AnotherBuildCorner/Relay_Switcher/Photos/Screenshot 2024-06-09 212933.png

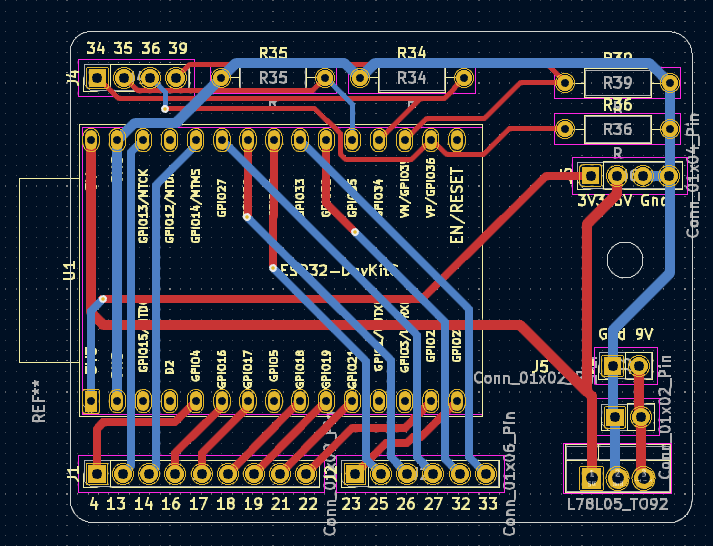
Photos/Screenshot 2024-06-09 212933.png
