AnotherBuildCorner/Relay_Switcher/Photos/Screenshot 2024-06-09 213035.png

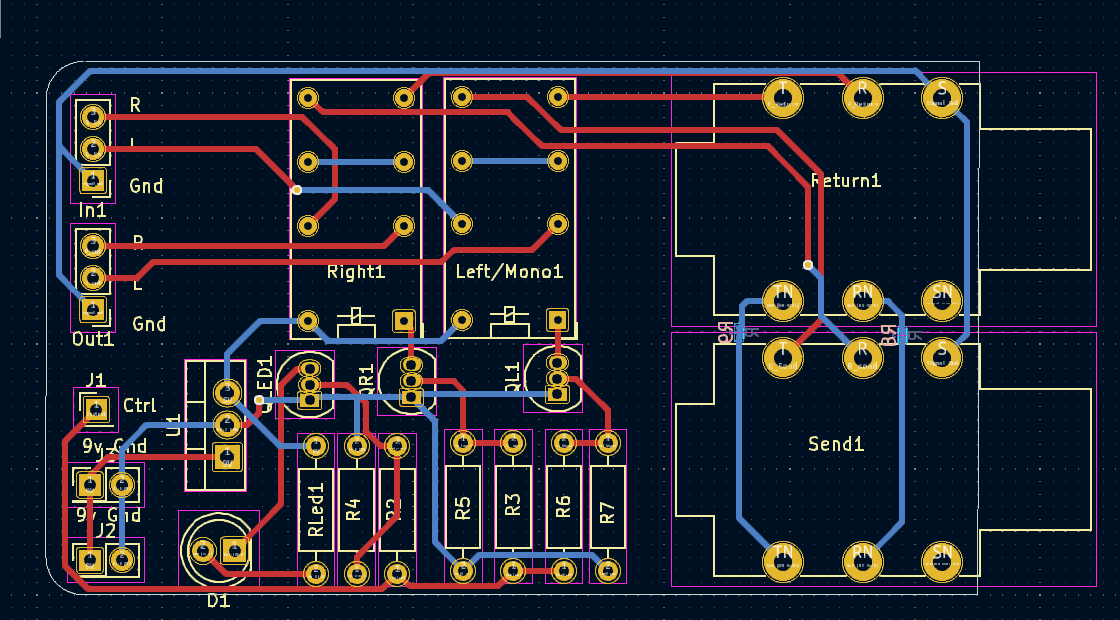
Photos/Screenshot 2024-06-09 213035.png
