AnotherBuildCorner/Relay_Switcher/Photos/Screenshot 2024-06-09 213115.png

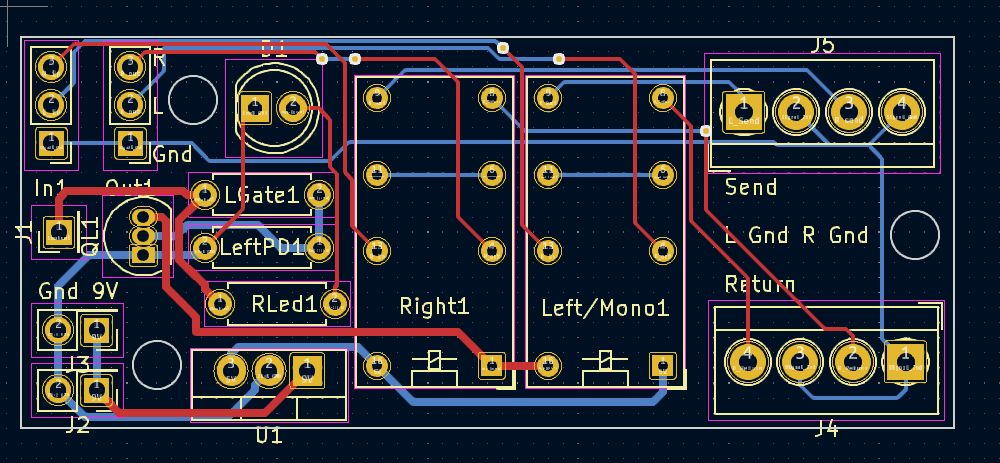
Photos/Screenshot 2024-06-09 213115.png
