AnotherBuildCorner/Relay_Switcher/Photos/Screenshot 2024-06-09 213131.png

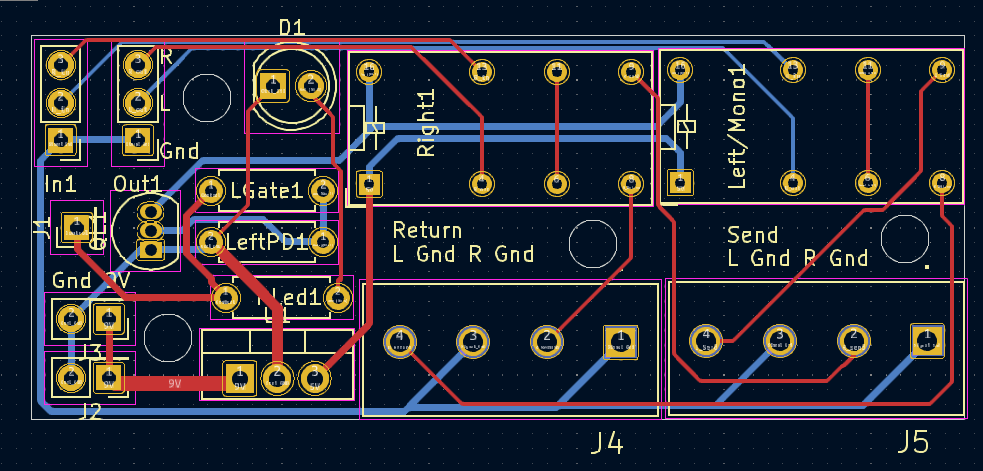
Photos/Screenshot 2024-06-09 213131.png
