AnotherBuildCorner/Relay_Switcher/Photos/V3 Jackless Input only.png

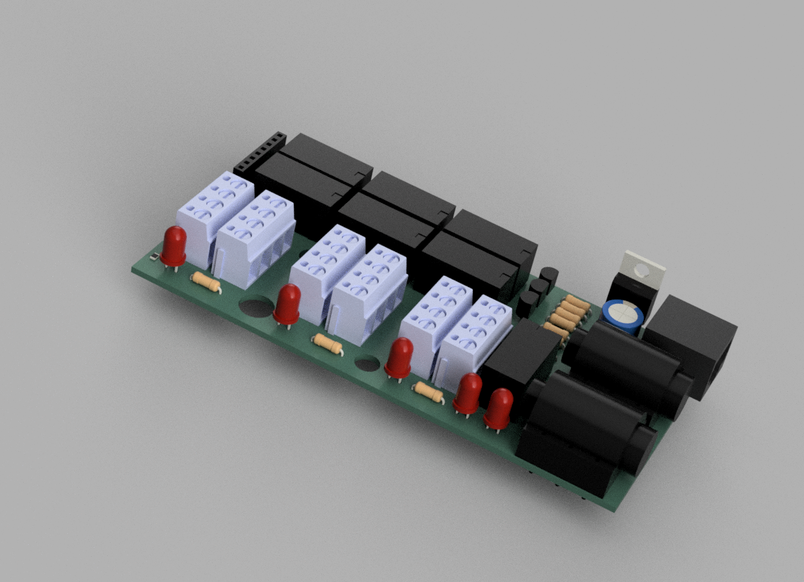
Photos/V3 Jackless Input only.png
