AnotherBuildCorner/Relay_Switcher/PCB's/Loop Board V3 Jackless/Loop Board 3 Jackless Input/Loop Board 3 Jackless Input.step

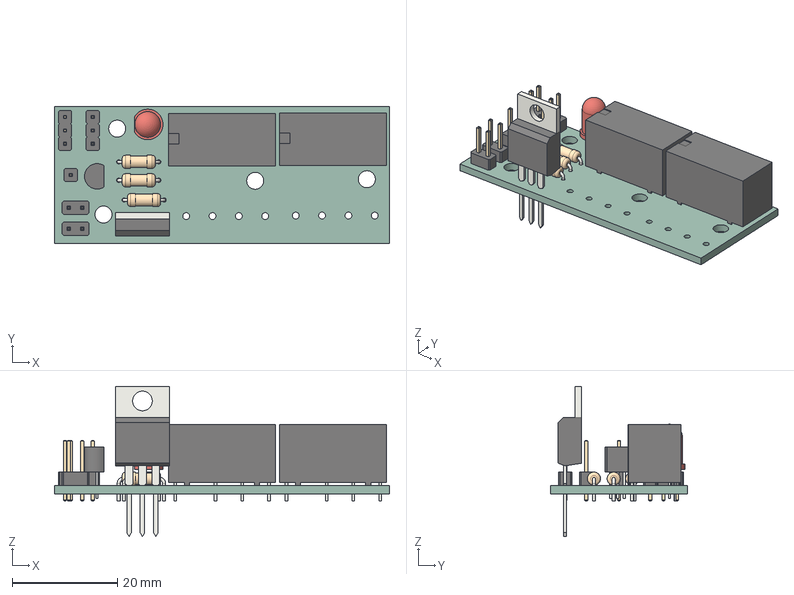
[picture p34: CAD file, 2024-06-10]
PCB's/Loop Board V3 Jackless/Loop Board 3 Jackless Input/Loop Board 3 Jackless Input.step
63.6 x 26.0 x 28.5 mm
PedalboardMain PCB
