AnotherBuildCorner/Relay_Switcher/3D Print Models/8 Switch Footswitch/8 bay back.stl

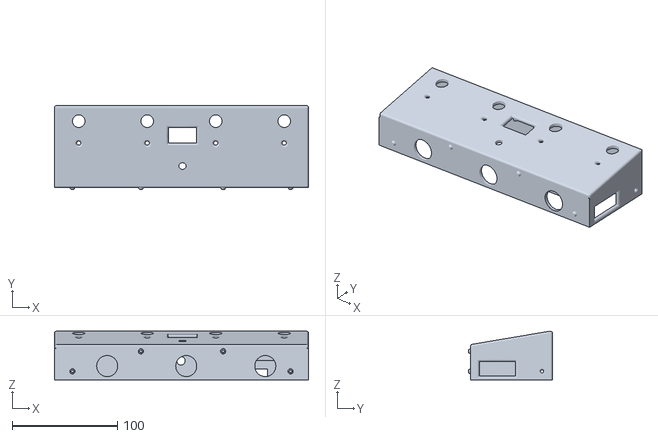
[picture p35: CAD file, 2024-07-15]
3D Print Models/8 Switch Footswitch/8 bay back.stl
241.0 x 80.0 x 46.0
