AnotherBuildCorner/Relay_Switcher/3D Print Models/V3 Jackless/6 Bay Long models/Base.stl

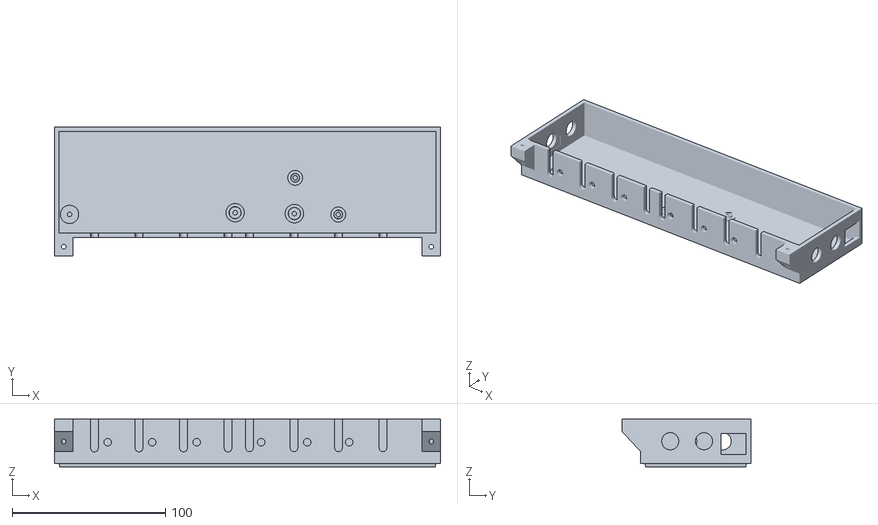
[picture p36: CAD file, 2024-07-15]
3D Print Models/V3 Jackless/6 Bay Long models/Base.stl
251.5 x 84.0 x 31.0
