AnotherBuildCorner/Relay_Switcher/3D Print Models/V3 Jackless/6 Bay Stack models/Lid.stl

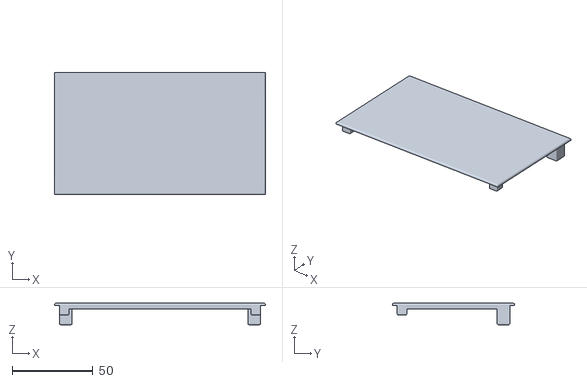
[picture p37: CAD file, 2024-07-15]
3D Print Models/V3 Jackless/6 Bay Stack models/Lid.stl
131.0 x 76.0 x 13.5
