AnotherBuildCorner/Relay_Switcher/3D Print Models/V3 Jackless/6 Bay Stack models/Bottom-output.stl

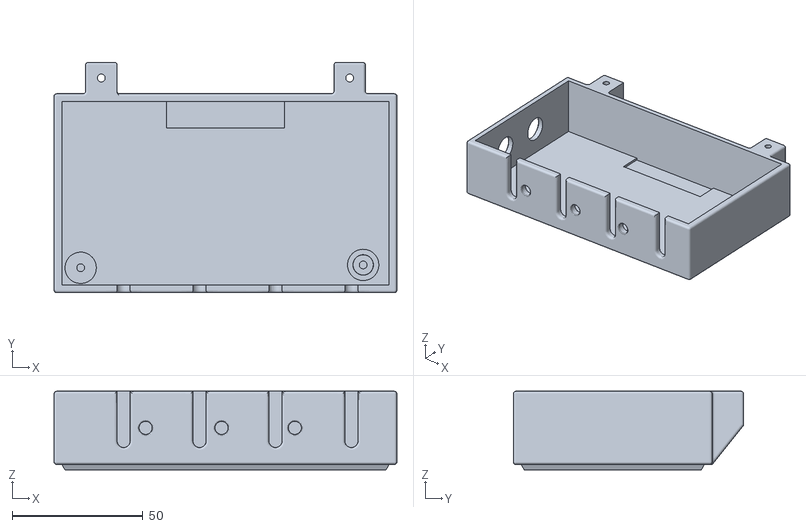
[picture p38: CAD file, 2024-07-15]
3D Print Models/V3 Jackless/6 Bay Stack models/Bottom-output.stl
131.0 x 88.0 x 30.0
