AnotherBuildCorner/Relay_Switcher/PCB's/8P breakout header/8P breakout header.kicad_pcb

## KiCad design PCB's/8P breakout header/8P breakout header.kicad_pcb (2024-06-09)

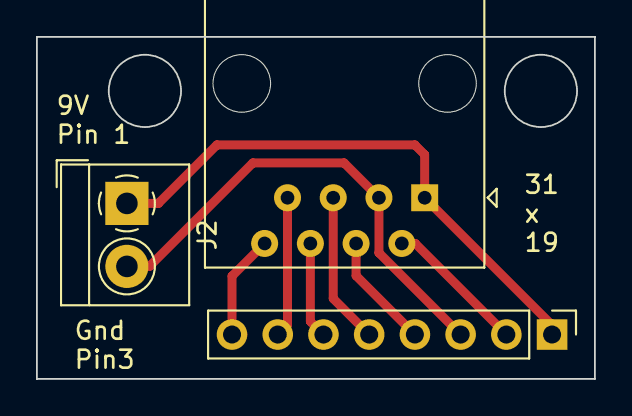
[picture p60: board PCB's/8P breakout header/8P breakout header.kicad_pcb from above]

Board: 2 copper layers, 31.0 x 19.0 mm, 3 parts (0 on the bottom side), 8 nets.

Parts:
J1: 8P8C; RJ45_Amphenol_54602-x08_Horizontal
J2: Screw_Terminal_01x02; TerminalBlock_4Ucon_1x02_P3.50mm_Horizontal
J4: Conn_01x08_Pin; PinHeader_1x08_P2.54mm_Vertical

Connections:
unnamed: J1.1, J2.1, J4.1
unnamed: J1.3, J2.2, J4.3
unnamed: J1.2, J4.2
unnamed: J1.4, J4.4
unnamed: J1.5, J4.5
unnamed: J1.6, J4.6
unnamed: J1.7, J4.7
unnamed: J1.8, J4.8
