AnotherBuildCorner/Relay_Switcher/PCB's/8P breakout header/8P breakout header panel/8P breakout header.kicad_pcb

## KiCad design PCB's/8P breakout header/8P breakout header panel/8P breakout header.kicad_pcb (2024-06-09)

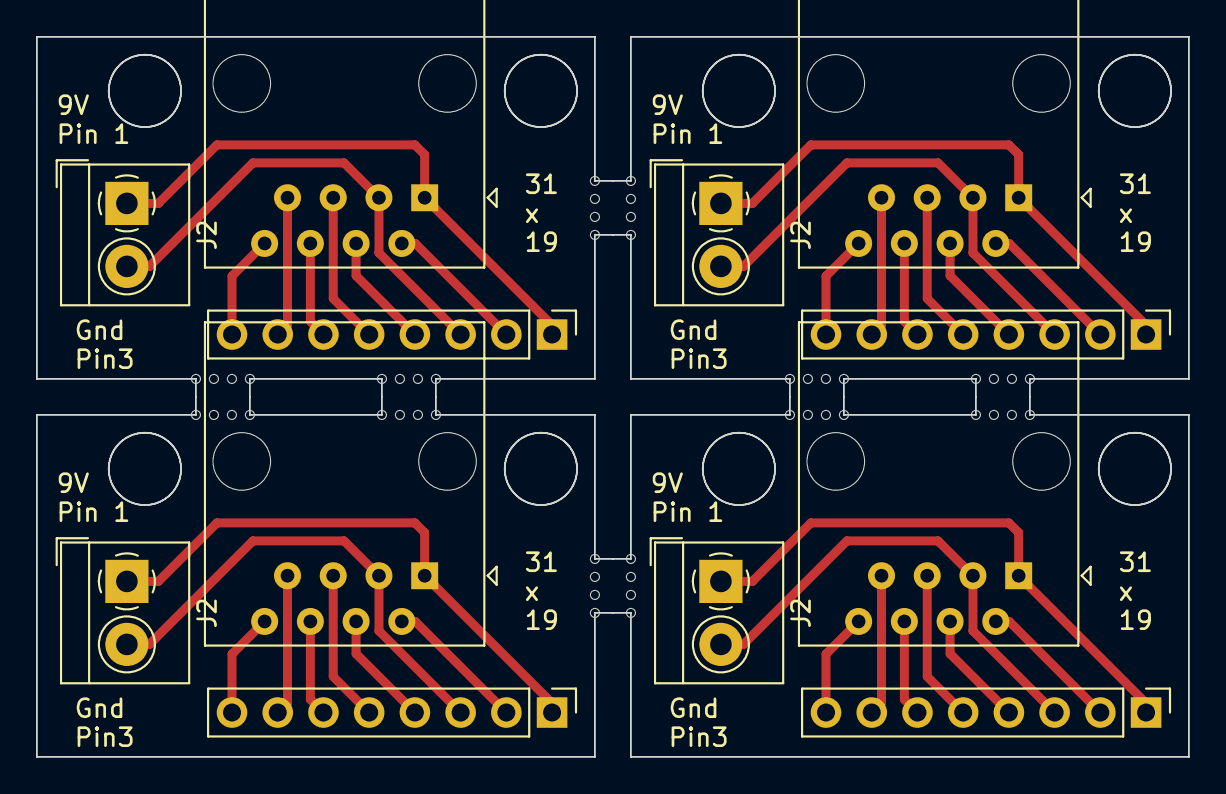
[picture p61: board PCB's/8P breakout header/8P breakout header panel/8P breakout header.… from above]

Board: 2 copper layers, 64.0 x 40.0 mm, 60 parts (0 on the bottom side), 32 nets.

Parts:
J1, J1#2, J1#3, J1#4: 8P8C; RJ45_Amphenol_54602-x08_Horizontal
J2, J2#2, J2#3, J2#4: Screw_Terminal_01x02; TerminalBlock_4Ucon_1x02_P3.50mm_Horizontal
J4, J4#2, J4#3, J4#4: Conn_01x08_Pin; PinHeader_1x08_P2.54mm_Vertical
KiKit_MB_1_1, KiKit_MB_1_2, KiKit_MB_1_3, KiKit_MB_1_4, KiKit_MB_2_1, KiKit_MB_2_2, KiKit_MB_2_3, KiKit_MB_2_4, KiKit_MB_3_1, KiKit_MB_3_2, KiKit_MB_3_3, KiKit_MB_3_4, KiKit_MB_4_1, KiKit_MB_4_2, KiKit_MB_4_3, KiKit_MB_4_4, KiKit_MB_5_1, KiKit_MB_5_2, KiKit_MB_5_3, KiKit_MB_5_4, KiKit_MB_6_1, KiKit_MB_6_2, KiKit_MB_6_3, KiKit_MB_6_4, KiKit_MB_7_1, KiKit_MB_7_2, KiKit_MB_7_3, KiKit_MB_7_4, KiKit_MB_8_1, KiKit_MB_8_2, KiKit_MB_8_3, KiKit_MB_8_4, KiKit_MB_9_1, KiKit_MB_9_2, KiKit_MB_9_3, KiKit_MB_9_4, KiKit_MB_10_1, KiKit_MB_10_2, KiKit_MB_10_3, KiKit_MB_10_4, KiKit_MB_11_1, KiKit_MB_11_2, KiKit_MB_11_3, KiKit_MB_11_4, KiKit_MB_12_1, KiKit_MB_12_2, KiKit_MB_12_3, KiKit_MB_12_4: NPTH

Connections:
Board_0-Net-(J2-Pin_1): J1#3.1, J2#3.1, J4#4.1
Board_0-Net-(J2-Pin_2): J1#3.3, J2#3.2, J4#4.3
Board_0-Net-(J4-Pin_2): J1#3.2, J4#4.2
Board_0-Net-(J4-Pin_4): J1#3.4, J4#4.4
Board_0-Net-(J4-Pin_5): J1#3.5, J4#4.5
Board_0-Net-(J4-Pin_6): J1#3.6, J4#4.6
Board_0-Net-(J4-Pin_7): J1#3.7, J4#4.7
Board_0-Net-(J4-Pin_8): J1#3.8, J4#4.8
Board_1-Net-(J2-Pin_1): J1#2.1, J2.1, J4#3.1
Board_1-Net-(J2-Pin_2): J1#2.3, J2.2, J4#3.3
Board_1-Net-(J4-Pin_2): J1#2.2, J4#3.2
Board_1-Net-(J4-Pin_4): J1#2.4, J4#3.4
Board_1-Net-(J4-Pin_5): J1#2.5, J4#3.5
Board_1-Net-(J4-Pin_6): J1#2.6, J4#3.6
Board_1-Net-(J4-Pin_7): J1#2.7, J4#3.7
Board_1-Net-(J4-Pin_8): J1#2.8, J4#3.8
Board_2-Net-(J2-Pin_1): J1.1, J2#4.1, J4.1
Board_2-Net-(J2-Pin_2): J1.3, J2#4.2, J4.3
Board_2-Net-(J4-Pin_2): J1.2, J4.2
Board_2-Net-(J4-Pin_4): J1.4, J4.4
Board_2-Net-(J4-Pin_5): J1.5, J4.5
Board_2-Net-(J4-Pin_6): J1.6, J4.6
Board_2-Net-(J4-Pin_7): J1.7, J4.7
Board_2-Net-(J4-Pin_8): J1.8, J4.8
Board_3-Net-(J2-Pin_1): J1#4.1, J2#2.1, J4#2.1
Board_3-Net-(J2-Pin_2): J1#4.3, J2#2.2, J4#2.3
Board_3-Net-(J4-Pin_2): J1#4.2, J4#2.2
Board_3-Net-(J4-Pin_4): J1#4.4, J4#2.4
Board_3-Net-(J4-Pin_5): J1#4.5, J4#2.5
Board_3-Net-(J4-Pin_6): J1#4.6, J4#2.6
Board_3-Net-(J4-Pin_7): J1#4.7, J4#2.7
Board_3-Net-(J4-Pin_8): J1#4.8, J4#2.8
