AnotherBuildCorner/Relay_Switcher/PCB's/Coms Board V1/PedalboardBrain.kicad_pcb

## KiCad design PCB's/Coms Board V1/PedalboardBrain.kicad_pcb (2024-06-09, an earlier design)

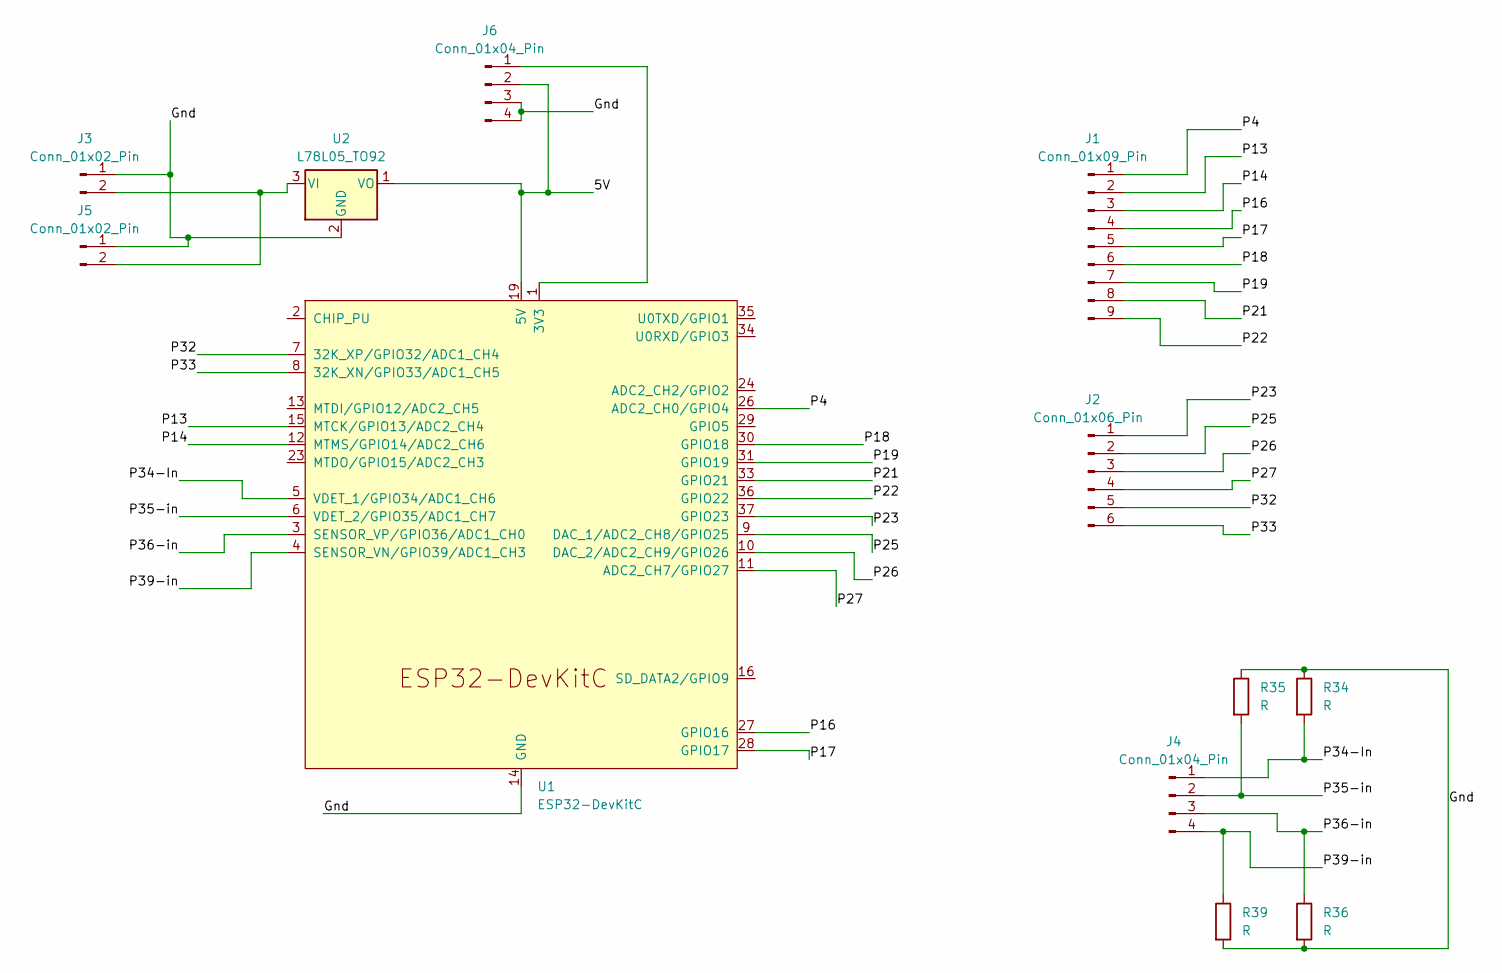
[picture p62: schematic PedalboardBrain.kicad_sch]

Parts:
J1: Conn_01x09_Pin; PinHeader_1x09_P2.54mm_Vertical
J2: Conn_01x06_Pin; PinHeader_1x06_P2.54mm_Vertical
J3, J5: Conn_01x02_Pin; PinHeader_1x02_P2.54mm_Vertical
J4, J6: Conn_01x04_Pin; PinHeader_1x04_P2.54mm_Vertical
R34, R35, R36, R39: R; R_Axial_DIN0207_L6.3mm_D2.5mm_P10.16mm_Horizontal
U1: ESP32-DevKitC; ESP32-DevKitC_30Pin
U2: L78L05_TO92; TO-220-3_Vertical

Connections:
/5V: J6.2, U1.19 (5V), U2.1 (VO)
/Gnd: J3.1, J5.1, J6.3, J6.4, R34.1, R35.1, R36.2, R39.2, U1.14 (GND), U1.32 (GND), U1.38 (GND), U2.2 (GND)
/P4: J1.1, U1.26 (ADC2_CH0/GPIO4)
/P13: J1.2, U1.15 (MTCK/GPIO13/ADC2_CH4)
/P14: J1.3, U1.12 (MTMS/GPIO14/ADC2_CH6)
/P16: J1.4, U1.27 (GPIO16)
/P17: J1.5, U1.28 (GPIO17)
/P18: J1.6, U1.30 (GPIO18)
/P19: J1.7, U1.31 (GPIO19)
/P21: J1.8, U1.33 (GPIO21)
/P22: J1.9, U1.36 (GPIO22)
/P23: J2.1, U1.37 (GPIO23)
/P25: J2.2, U1.9 (DAC_1/ADC2_CH8/GPIO25)
/P26: J2.3, U1.10 (DAC_2/ADC2_CH9/GPIO26)
/P27: J2.4, U1.11 (ADC2_CH7/GPIO27)
/P32: J2.5, U1.7 (32K_XP/GPIO32/ADC1_CH4)
/P33: J2.6, U1.8 (32K_XN/GPIO33/ADC1_CH5)
/P34-In: J4.1, R34.2, U1.5 (VDET_1/GPIO34/ADC1_CH6)
/P35-in: J4.2, R35.2, U1.6 (VDET_2/GPIO35/ADC1_CH7)
/P36-in: J4.3, R36.1, U1.3 (SENSOR_VP/GPIO36/ADC1_CH0)
/P39-in: J4.4, R39.1, U1.4 (SENSOR_VN/GPIO39/ADC1_CH3)
unnamed: J3.2, J5.2, U2.3 (VI)
unnamed: J6.1, U1.1 (3V3)

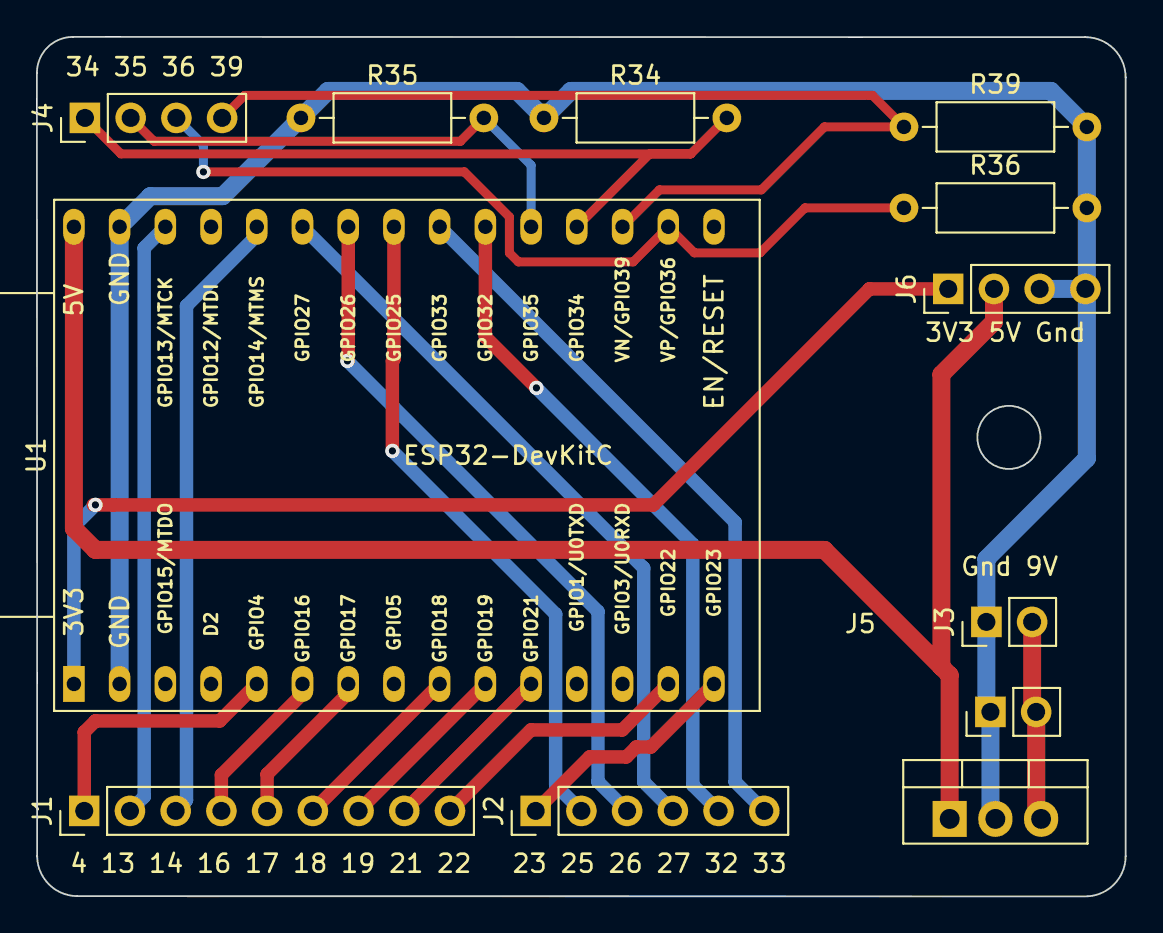
[picture p63: board PedalboardBrain.kicad_pcb from above]

Board: 2 copper layers, 60.5 x 47.8 mm, 12 parts (0 on the bottom side), 23 nets.
