AnotherBuildCorner/Relay_Switcher/PCB's/Coms Board V2/Coms Board V2.kicad_pcb

## KiCad design PCB's/Coms Board V2/Coms Board V2.kicad_pcb (2024-06-08)

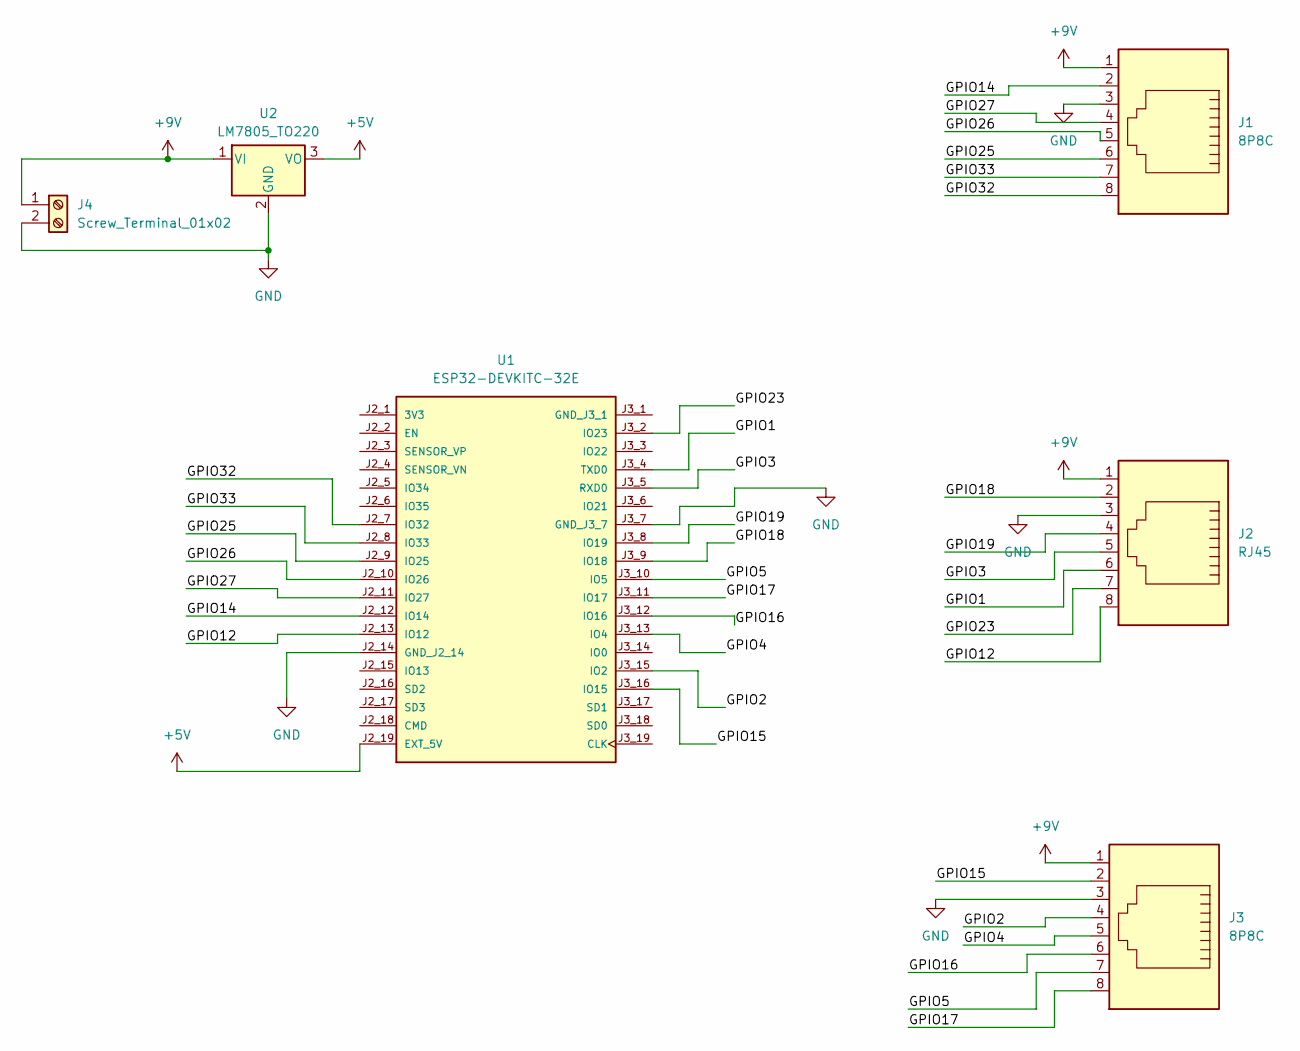
[picture p64: schematic Coms Board V2.kicad_sch]

Parts:
J1, J3: 8P8C; RJ45_Amphenol_54602-x08_Horizontal
J2: RJ45; RJ45_Amphenol_54602-x08_Horizontal
J4: Screw_Terminal_01x02; TerminalBlock_Altech_AK300-2_P5.00mm
U1: ESP32-DEVKITC-32E; MODULE_ESP32-DEVKITC-32E; PARTREV 1.4
U2: LM7805_TO220; TO-220-3_Vertical

Connections:
+5V: U1.J2_19 (EXT_5V), U2.3 (VO)
+9V: J1.1, J2.1, J3.1, J4.1, U2.1 (VI)
/GPIO1: J2.6, U1.J3_4 (TXD0)
/GPIO2: J3.4, U1.J3_15 (IO2)
/GPIO3: J2.5, U1.J3_5 (RXD0)
/GPIO4: J3.5, U1.J3_13 (IO4)
/GPIO5: J3.7, U1.J3_10 (IO5)
/GPIO12: J2.8, U1.J2_13 (IO12)
/GPIO14: J1.2, U1.J2_12 (IO14)
/GPIO15: J3.2, U1.J3_16 (IO15)
/GPIO16: J3.6, U1.J3_12 (IO16)
/GPIO17: J3.8, U1.J3_11 (IO17)
/GPIO18: J2.2, U1.J3_9 (IO18)
/GPIO19: J2.4, U1.J3_8 (IO19)
/GPIO23: J2.7, U1.J3_2 (IO23)
/GPIO25: J1.6, U1.J2_9 (IO25)
/GPIO26: J1.5, U1.J2_10 (IO26)
/GPIO27: J1.4, U1.J2_11 (IO27)
/GPIO32: J1.8, U1.J2_7 (IO32)
/GPIO33: J1.7, U1.J2_8 (IO33)
GND: J1.3, J2.3, J3.3, J4.2, U1.J2_14 (GND_J2_14), U1.J3_7 (GND_J3_7), U2.2 (GND)

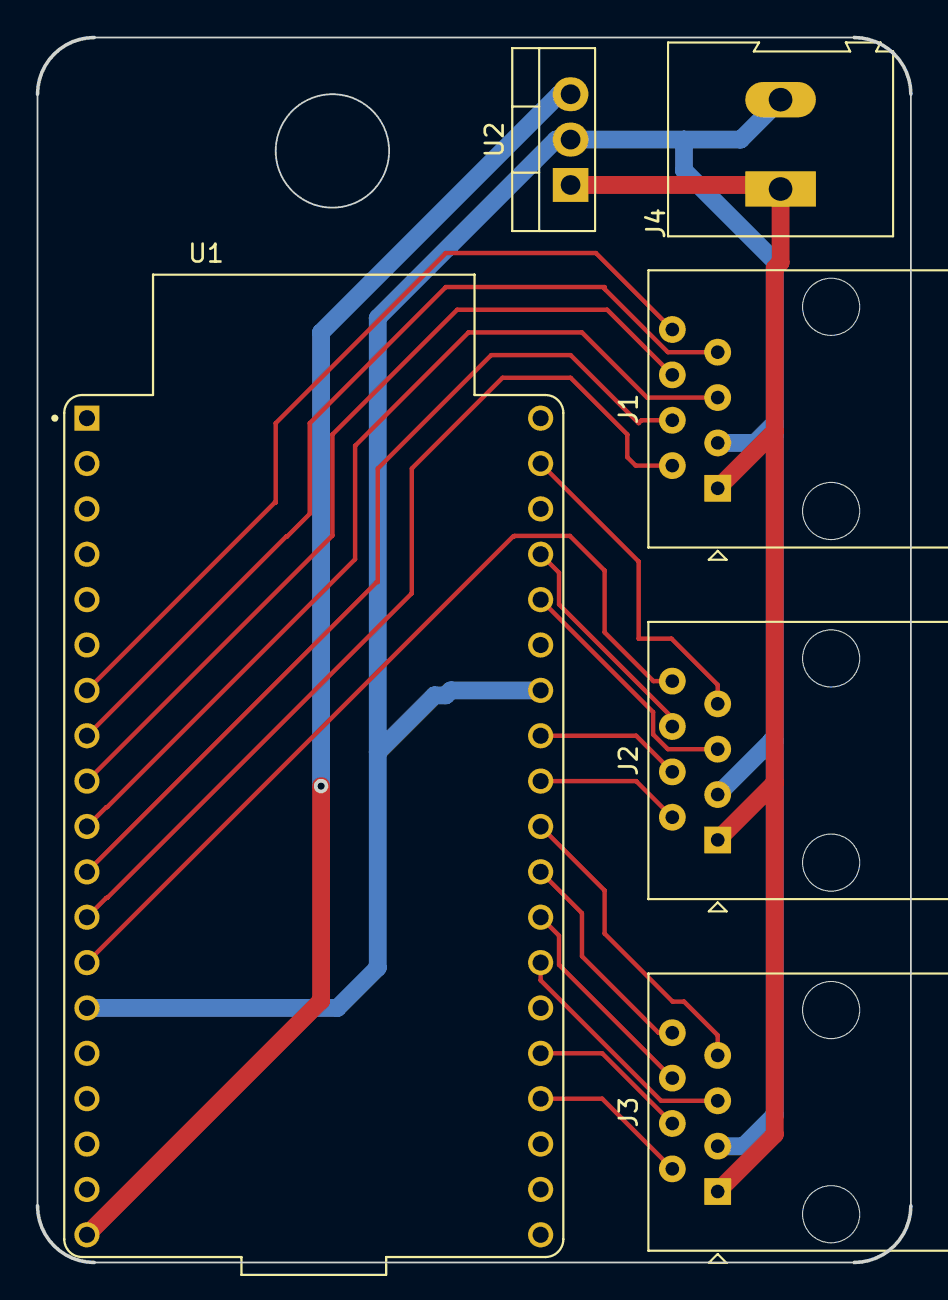
[picture p65: board Coms Board V2.kicad_pcb from above]

Board: 2 copper layers, 48.9 x 68.6 mm, 6 parts (0 on the bottom side), 21 nets.
