AnotherBuildCorner/Relay_Switcher/PCB's/DIP16 Adapt/DIP16 Adapt Panel.kicad_pcb

## KiCad design PCB's/DIP16 Adapt/DIP16 Adapt Panel.kicad_pcb (2024-08-11)

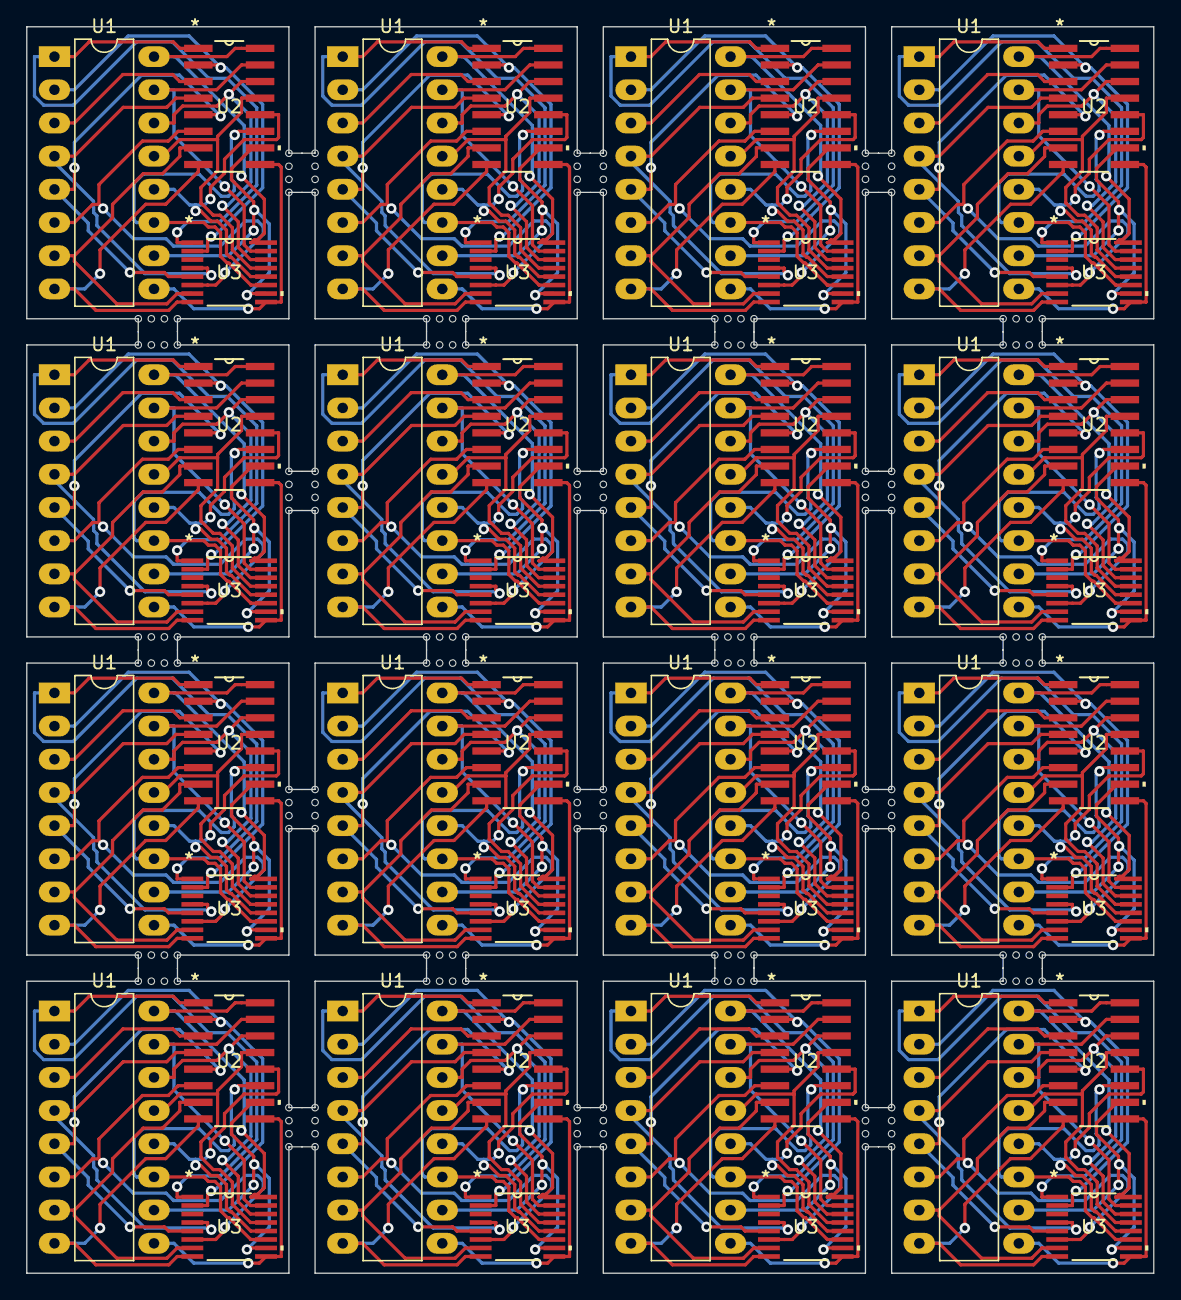
[picture p66: board DIP16 Adapt Panel.kicad_pcb from above]

Board: 2 copper layers, 86.3 x 95.4 mm, 240 parts (0 on the bottom side), 256 nets.

Parts:
KiKit_MB_1_1, KiKit_MB_1_2, KiKit_MB_1_3, KiKit_MB_1_4, KiKit_MB_2_1, KiKit_MB_2_2, KiKit_MB_2_3, KiKit_MB_2_4, KiKit_MB_3_1, KiKit_MB_3_2, KiKit_MB_3_3, KiKit_MB_3_4, KiKit_MB_4_1, KiKit_MB_4_2, KiKit_MB_4_3, KiKit_MB_4_4, KiKit_MB_5_1, KiKit_MB_5_2, KiKit_MB_5_3, KiKit_MB_5_4, KiKit_MB_6_1, KiKit_MB_6_2, KiKit_MB_6_3, KiKit_MB_6_4, KiKit_MB_7_1, KiKit_MB_7_2, KiKit_MB_7_3, KiKit_MB_7_4, KiKit_MB_8_1, KiKit_MB_8_2, KiKit_MB_8_3, KiKit_MB_8_4, KiKit_MB_9_1, KiKit_MB_9_2, KiKit_MB_9_3, KiKit_MB_9_4, KiKit_MB_10_1, KiKit_MB_10_2, KiKit_MB_10_3, KiKit_MB_10_4, KiKit_MB_11_1, KiKit_MB_11_2, KiKit_MB_11_3, KiKit_MB_11_4, KiKit_MB_12_1, KiKit_MB_12_2, KiKit_MB_12_3, KiKit_MB_12_4, KiKit_MB_13_1, KiKit_MB_13_2, KiKit_MB_13_3, KiKit_MB_13_4, KiKit_MB_14_1, KiKit_MB_14_2, KiKit_MB_14_3, KiKit_MB_14_4, KiKit_MB_15_1, KiKit_MB_15_2, KiKit_MB_15_3, KiKit_MB_15_4, KiKit_MB_16_1, KiKit_MB_16_2, KiKit_MB_16_3, KiKit_MB_16_4, KiKit_MB_17_1, KiKit_MB_17_2, KiKit_MB_17_3, KiKit_MB_17_4, KiKit_MB_18_1, KiKit_MB_18_2, KiKit_MB_18_3, KiKit_MB_18_4, KiKit_MB_19_1, KiKit_MB_19_2, KiKit_MB_19_3, KiKit_MB_19_4, KiKit_MB_20_1, KiKit_MB_20_2, KiKit_MB_20_3, KiKit_MB_20_4, KiKit_MB_21_1, KiKit_MB_21_2, KiKit_MB_21_3, KiKit_MB_21_4, KiKit_MB_22_1, KiKit_MB_22_2, KiKit_MB_22_3, KiKit_MB_22_4, KiKit_MB_23_1, KiKit_MB_23_2, KiKit_MB_23_3, KiKit_MB_23_4, KiKit_MB_24_1, KiKit_MB_24_2, KiKit_MB_24_3, KiKit_MB_24_4, KiKit_MB_25_1, KiKit_MB_25_2, KiKit_MB_25_3, KiKit_MB_25_4, KiKit_MB_26_1, KiKit_MB_26_2, KiKit_MB_26_3, KiKit_MB_26_4, KiKit_MB_27_1, KiKit_MB_27_2, KiKit_MB_27_3, KiKit_MB_27_4, KiKit_MB_28_1, KiKit_MB_28_2, KiKit_MB_28_3, KiKit_MB_28_4, KiKit_MB_29_1, KiKit_MB_29_2, KiKit_MB_29_3, KiKit_MB_29_4, KiKit_MB_30_1, KiKit_MB_30_2, KiKit_MB_30_3, KiKit_MB_30_4, KiKit_MB_31_1, KiKit_MB_31_2, KiKit_MB_31_3, KiKit_MB_31_4, KiKit_MB_32_1, KiKit_MB_32_2, KiKit_MB_32_3, KiKit_MB_32_4, KiKit_MB_33_1, KiKit_MB_33_2, KiKit_MB_33_3, KiKit_MB_33_4, KiKit_MB_34_1, KiKit_MB_34_2, KiKit_MB_34_3, KiKit_MB_34_4, KiKit_MB_35_1, KiKit_MB_35_2, KiKit_MB_35_3, KiKit_MB_35_4, KiKit_MB_36_1, KiKit_MB_36_2, KiKit_MB_36_3, KiKit_MB_36_4, KiKit_MB_37_1, KiKit_MB_37_2, KiKit_MB_37_3, KiKit_MB_37_4, KiKit_MB_38_1, KiKit_MB_38_2, KiKit_MB_38_3, KiKit_MB_38_4, KiKit_MB_39_1, KiKit_MB_39_2, KiKit_MB_39_3, KiKit_MB_39_4, KiKit_MB_40_1, KiKit_MB_40_2, KiKit_MB_40_3, KiKit_MB_40_4, KiKit_MB_41_1, KiKit_MB_41_2, KiKit_MB_41_3, KiKit_MB_41_4, KiKit_MB_42_1, KiKit_MB_42_2, KiKit_MB_42_3, KiKit_MB_42_4, KiKit_MB_43_1, KiKit_MB_43_2, KiKit_MB_43_3, KiKit_MB_43_4, KiKit_MB_44_1, KiKit_MB_44_2, KiKit_MB_44_3, KiKit_MB_44_4, KiKit_MB_45_1, KiKit_MB_45_2, KiKit_MB_45_3, KiKit_MB_45_4, KiKit_MB_46_1, KiKit_MB_46_2, KiKit_MB_46_3, KiKit_MB_46_4, KiKit_MB_47_1, KiKit_MB_47_2, KiKit_MB_47_3, KiKit_MB_47_4, KiKit_MB_48_1, KiKit_MB_48_2, KiKit_MB_48_3, KiKit_MB_48_4: NPTH
U1, U1#2, U1#3, U1#4, U1#5, U1#6, U1#7, U1#8, U1#9, U1#10, U1#11, U1#12, U1#13, U1#14, U1#15, U1#16: CD74HC4051M96; DIP-16_W7.62mm_LongPads
U2, U2#2, U2#3, U2#4, U2#5, U2#6, U2#7, U2#8, U2#9, U2#10, U2#11, U2#12, U2#13, U2#14, U2#15, U2#16: CD74HC4051M96; D16
U3, U3#2, U3#3, U3#4, U3#5, U3#6, U3#7, U3#8, U3#9, U3#10, U3#11, U3#12, U3#13, U3#14, U3#15, U3#16: CD74HC4051M96; PW16

Connections:
Board_0-Net-(U1-*E): U1#5.6 (*E), U2#8.6 (*E), U3#13.6 (*E)
Board_0-Net-(U1-A0): U1#5.13 (A0), U2#8.13 (A0), U3#13.13 (A0)
Board_0-Net-(U1-A1): U1#5.14 (A1), U2#8.14 (A1), U3#13.14 (A1)
Board_0-Net-(U1-A2): U1#5.15 (A2), U2#8.15 (A2), U3#13.15 (A2)
Board_0-Net-(U1-A3): U1#5.12 (A3), U2#8.12 (A3), U3#13.12 (A3)
Board_0-Net-(U1-A4): U1#5.1 (A4), U2#8.1 (A4), U3#13.1 (A4)
Board_0-Net-(U1-A5): U1#5.5 (A5), U2#8.5 (A5), U3#13.5 (A5)
Board_0-Net-(U1-A6): U1#5.2 (A6), U2#8.2 (A6), U3#13.2 (A6)
Board_0-Net-(U1-A7): U1#5.4 (A7), U2#8.4 (A7), U3#13.4 (A7)
Board_0-Net-(U1-A): U1#5.3 (A), U2#8.3 (A), U3#13.3 (A)
Board_0-Net-(U1-GND): U1#5.8 (GND), U2#8.8 (GND), U3#13.8 (GND)
Board_0-Net-(U1-S0): U1#5.11 (S0), U2#8.11 (S0), U3#13.11 (S0)
Board_0-Net-(U1-S1): U1#5.10 (S1), U2#8.10 (S1), U3#13.10 (S1)
Board_0-Net-(U1-S2): U1#5.9 (S2), U2#8.9 (S2), U3#13.9 (S2)
Board_0-Net-(U1-VCC): U1#5.16 (VCC), U2#8.16 (VCC), U3#13.16 (VCC)
Board_0-Net-(U1-VEE): U1#5.7 (VEE), U2#8.7 (VEE), U3#13.7 (VEE)
Board_1-Net-(U1-*E): U1#10.6 (*E), U2#9.6 (*E), U3#6.6 (*E)
Board_1-Net-(U1-A0): U1#10.13 (A0), U2#9.13 (A0), U3#6.13 (A0)
Board_1-Net-(U1-A1): U1#10.14 (A1), U2#9.14 (A1), U3#6.14 (A1)
Board_1-Net-(U1-A2): U1#10.15 (A2), U2#9.15 (A2), U3#6.15 (A2)
Board_1-Net-(U1-A3): U1#10.12 (A3), U2#9.12 (A3), U3#6.12 (A3)
Board_1-Net-(U1-A4): U1#10.1 (A4), U2#9.1 (A4), U3#6.1 (A4)
Board_1-Net-(U1-A5): U1#10.5 (A5), U2#9.5 (A5), U3#6.5 (A5)
Board_1-Net-(U1-A6): U1#10.2 (A6), U2#9.2 (A6), U3#6.2 (A6)
Board_1-Net-(U1-A7): U1#10.4 (A7), U2#9.4 (A7), U3#6.4 (A7)
Board_1-Net-(U1-A): U1#10.3 (A), U2#9.3 (A), U3#6.3 (A)
Board_1-Net-(U1-GND): U1#10.8 (GND), U2#9.8 (GND), U3#6.8 (GND)
Board_1-Net-(U1-S0): U1#10.11 (S0), U2#9.11 (S0), U3#6.11 (S0)
Board_1-Net-(U1-S1): U1#10.10 (S1), U2#9.10 (S1), U3#6.10 (S1)
Board_1-Net-(U1-S2): U1#10.9 (S2), U2#9.9 (S2), U3#6.9 (S2)
Board_1-Net-(U1-VCC): U1#10.16 (VCC), U2#9.16 (VCC), U3#6.16 (VCC)
Board_1-Net-(U1-VEE): U1#10.7 (VEE), U2#9.7 (VEE), U3#6.7 (VEE)
Board_2-Net-(U1-*E): U1#16.6 (*E), U2#14.6 (*E), U3.6 (*E)
Board_2-Net-(U1-A0): U1#16.13 (A0), U2#14.13 (A0), U3.13 (A0)
Board_2-Net-(U1-A1): U1#16.14 (A1), U2#14.14 (A1), U3.14 (A1)
Board_2-Net-(U1-A2): U1#16.15 (A2), U2#14.15 (A2), U3.15 (A2)
Board_2-Net-(U1-A3): U1#16.12 (A3), U2#14.12 (A3), U3.12 (A3)
Board_2-Net-(U1-A4): U1#16.1 (A4), U2#14.1 (A4), U3.1 (A4)
Board_2-Net-(U1-A5): U1#16.5 (A5), U2#14.5 (A5), U3.5 (A5)
Board_2-Net-(U1-A6): U1#16.2 (A6), U2#14.2 (A6), U3.2 (A6)
Board_2-Net-(U1-A7): U1#16.4 (A7), U2#14.4 (A7), U3.4 (A7)
Board_2-Net-(U1-A): U1#16.3 (A), U2#14.3 (A), U3.3 (A)
Board_2-Net-(U1-GND): U1#16.8 (GND), U2#14.8 (GND), U3.8 (GND)
Board_2-Net-(U1-S0): U1#16.11 (S0), U2#14.11 (S0), U3.11 (S0)
Board_2-Net-(U1-S1): U1#16.10 (S1), U2#14.10 (S1), U3.10 (S1)
Board_2-Net-(U1-S2): U1#16.9 (S2), U2#14.9 (S2), U3.9 (S2)
Board_2-Net-(U1-VCC): U1#16.16 (VCC), U2#14.16 (VCC), U3.16 (VCC)
Board_2-Net-(U1-VEE): U1#16.7 (VEE), U2#14.7 (VEE), U3.7 (VEE)
Board_3-Net-(U1-*E): U1#2.6 (*E), U2#12.6 (*E), U3#11.6 (*E)
Board_3-Net-(U1-A0): U1#2.13 (A0), U2#12.13 (A0), U3#11.13 (A0)
Board_3-Net-(U1-A1): U1#2.14 (A1), U2#12.14 (A1), U3#11.14 (A1)
Board_3-Net-(U1-A2): U1#2.15 (A2), U2#12.15 (A2), U3#11.15 (A2)
Board_3-Net-(U1-A3): U1#2.12 (A3), U2#12.12 (A3), U3#11.12 (A3)
Board_3-Net-(U1-A4): U1#2.1 (A4), U2#12.1 (A4), U3#11.1 (A4)
Board_3-Net-(U1-A5): U1#2.5 (A5), U2#12.5 (A5), U3#11.5 (A5)
Board_3-Net-(U1-A6): U1#2.2 (A6), U2#12.2 (A6), U3#11.2 (A6)
Board_3-Net-(U1-A7): U1#2.4 (A7), U2#12.4 (A7), U3#11.4 (A7)
Board_3-Net-(U1-A): U1#2.3 (A), U2#12.3 (A), U3#11.3 (A)
Board_3-Net-(U1-GND): U1#2.8 (GND), U2#12.8 (GND), U3#11.8 (GND)
Board_3-Net-(U1-S0): U1#2.11 (S0), U2#12.11 (S0), U3#11.11 (S0)
Board_3-Net-(U1-S1): U1#2.10 (S1), U2#12.10 (S1), U3#11.10 (S1)
Board_3-Net-(U1-S2): U1#2.9 (S2), U2#12.9 (S2), U3#11.9 (S2)
Board_3-Net-(U1-VCC): U1#2.16 (VCC), U2#12.16 (VCC), U3#11.16 (VCC)
Board_3-Net-(U1-VEE): U1#2.7 (VEE), U2#12.7 (VEE), U3#11.7 (VEE)
Board_4-Net-(U1-*E): U1#3.6 (*E), U2.6 (*E), U3#7.6 (*E)
Board_4-Net-(U1-A0): U1#3.13 (A0), U2.13 (A0), U3#7.13 (A0)
Board_4-Net-(U1-A1): U1#3.14 (A1), U2.14 (A1), U3#7.14 (A1)
Board_4-Net-(U1-A2): U1#3.15 (A2), U2.15 (A2), U3#7.15 (A2)
Board_4-Net-(U1-A3): U1#3.12 (A3), U2.12 (A3), U3#7.12 (A3)
Board_4-Net-(U1-A4): U1#3.1 (A4), U2.1 (A4), U3#7.1 (A4)
Board_4-Net-(U1-A5): U1#3.5 (A5), U2.5 (A5), U3#7.5 (A5)
Board_4-Net-(U1-A6): U1#3.2 (A6), U2.2 (A6), U3#7.2 (A6)
Board_4-Net-(U1-A7): U1#3.4 (A7), U2.4 (A7), U3#7.4 (A7)
Board_4-Net-(U1-A): U1#3.3 (A), U2.3 (A), U3#7.3 (A)
Board_4-Net-(U1-GND): U1#3.8 (GND), U2.8 (GND), U3#7.8 (GND)
Board_4-Net-(U1-S0): U1#3.11 (S0), U2.11 (S0), U3#7.11 (S0)
Board_4-Net-(U1-S1): U1#3.10 (S1), U2.10 (S1), U3#7.10 (S1)
Board_4-Net-(U1-S2): U1#3.9 (S2), U2.9 (S2), U3#7.9 (S2)
Board_4-Net-(U1-VCC): U1#3.16 (VCC), U2.16 (VCC), U3#7.16 (VCC)
Board_4-Net-(U1-VEE): U1#3.7 (VEE), U2.7 (VEE), U3#7.7 (VEE)
Board_5-Net-(U1-*E): U1#11.6 (*E), U2#7.6 (*E), U3#14.6 (*E)
Board_5-Net-(U1-A0): U1#11.13 (A0), U2#7.13 (A0), U3#14.13 (A0)
Board_5-Net-(U1-A1): U1#11.14 (A1), U2#7.14 (A1), U3#14.14 (A1)
Board_5-Net-(U1-A2): U1#11.15 (A2), U2#7.15 (A2), U3#14.15 (A2)
Board_5-Net-(U1-A3): U1#11.12 (A3), U2#7.12 (A3), U3#14.12 (A3)
Board_5-Net-(U1-A4): U1#11.1 (A4), U2#7.1 (A4), U3#14.1 (A4)
Board_5-Net-(U1-A5): U1#11.5 (A5), U2#7.5 (A5), U3#14.5 (A5)
Board_5-Net-(U1-A6): U1#11.2 (A6), U2#7.2 (A6), U3#14.2 (A6)
Board_5-Net-(U1-A7): U1#11.4 (A7), U2#7.4 (A7), U3#14.4 (A7)
Board_5-Net-(U1-A): U1#11.3 (A), U2#7.3 (A), U3#14.3 (A)
Board_5-Net-(U1-GND): U1#11.8 (GND), U2#7.8 (GND), U3#14.8 (GND)
Board_5-Net-(U1-S0): U1#11.11 (S0), U2#7.11 (S0), U3#14.11 (S0)
Board_5-Net-(U1-S1): U1#11.10 (S1), U2#7.10 (S1), U3#14.10 (S1)
Board_5-Net-(U1-S2): U1#11.9 (S2), U2#7.9 (S2), U3#14.9 (S2)
Board_5-Net-(U1-VCC): U1#11.16 (VCC), U2#7.16 (VCC), U3#14.16 (VCC)
Board_5-Net-(U1-VEE): U1#11.7 (VEE), U2#7.7 (VEE), U3#14.7 (VEE)
Board_6-Net-(U1-*E): U1#14.6 (*E), U2#6.6 (*E), U3#9.6 (*E)
Board_6-Net-(U1-A0): U1#14.13 (A0), U2#6.13 (A0), U3#9.13 (A0)
Board_6-Net-(U1-A1): U1#14.14 (A1), U2#6.14 (A1), U3#9.14 (A1)
Board_6-Net-(U1-A2): U1#14.15 (A2), U2#6.15 (A2), U3#9.15 (A2)
Board_6-Net-(U1-A3): U1#14.12 (A3), U2#6.12 (A3), U3#9.12 (A3)
Board_6-Net-(U1-A4): U1#14.1 (A4), U2#6.1 (A4), U3#9.1 (A4)
Board_6-Net-(U1-A5): U1#14.5 (A5), U2#6.5 (A5), U3#9.5 (A5)
Board_6-Net-(U1-A6): U1#14.2 (A6), U2#6.2 (A6), U3#9.2 (A6)
Board_6-Net-(U1-A7): U1#14.4 (A7), U2#6.4 (A7), U3#9.4 (A7)
Board_6-Net-(U1-A): U1#14.3 (A), U2#6.3 (A), U3#9.3 (A)
Board_6-Net-(U1-GND): U1#14.8 (GND), U2#6.8 (GND), U3#9.8 (GND)
Board_6-Net-(U1-S0): U1#14.11 (S0), U2#6.11 (S0), U3#9.11 (S0)
Board_6-Net-(U1-S1): U1#14.10 (S1), U2#6.10 (S1), U3#9.10 (S1)
Board_6-Net-(U1-S2): U1#14.9 (S2), U2#6.9 (S2), U3#9.9 (S2)
Board_6-Net-(U1-VCC): U1#14.16 (VCC), U2#6.16 (VCC), U3#9.16 (VCC)
Board_6-Net-(U1-VEE): U1#14.7 (VEE), U2#6.7 (VEE), U3#9.7 (VEE)
Board_7-Net-(U1-*E): U1#7.6 (*E), U2#4.6 (*E), U3#5.6 (*E)
Board_7-Net-(U1-A0): U1#7.13 (A0), U2#4.13 (A0), U3#5.13 (A0)
Board_7-Net-(U1-A1): U1#7.14 (A1), U2#4.14 (A1), U3#5.14 (A1)
Board_7-Net-(U1-A2): U1#7.15 (A2), U2#4.15 (A2), U3#5.15 (A2)
Board_7-Net-(U1-A3): U1#7.12 (A3), U2#4.12 (A3), U3#5.12 (A3)
Board_7-Net-(U1-A4): U1#7.1 (A4), U2#4.1 (A4), U3#5.1 (A4)
Board_7-Net-(U1-A5): U1#7.5 (A5), U2#4.5 (A5), U3#5.5 (A5)
Board_7-Net-(U1-A6): U1#7.2 (A6), U2#4.2 (A6), U3#5.2 (A6)
Board_7-Net-(U1-A7): U1#7.4 (A7), U2#4.4 (A7), U3#5.4 (A7)
Board_7-Net-(U1-A): U1#7.3 (A), U2#4.3 (A), U3#5.3 (A)
Board_7-Net-(U1-GND): U1#7.8 (GND), U2#4.8 (GND), U3#5.8 (GND)
Board_7-Net-(U1-S0): U1#7.11 (S0), U2#4.11 (S0), U3#5.11 (S0)
Board_7-Net-(U1-S1): U1#7.10 (S1), U2#4.10 (S1), U3#5.10 (S1)
Board_7-Net-(U1-S2): U1#7.9 (S2), U2#4.9 (S2), U3#5.9 (S2)
Board_7-Net-(U1-VCC): U1#7.16 (VCC), U2#4.16 (VCC), U3#5.16 (VCC)
Board_7-Net-(U1-VEE): U1#7.7 (VEE), U2#4.7 (VEE), U3#5.7 (VEE)
Board_8-Net-(U1-*E): U1#13.6 (*E), U2#11.6 (*E), U3#10.6 (*E)
Board_8-Net-(U1-A0): U1#13.13 (A0), U2#11.13 (A0), U3#10.13 (A0)
Board_8-Net-(U1-A1): U1#13.14 (A1), U2#11.14 (A1), U3#10.14 (A1)
Board_8-Net-(U1-A2): U1#13.15 (A2), U2#11.15 (A2), U3#10.15 (A2)
Board_8-Net-(U1-A3): U1#13.12 (A3), U2#11.12 (A3), U3#10.12 (A3)
Board_8-Net-(U1-A4): U1#13.1 (A4), U2#11.1 (A4), U3#10.1 (A4)
Board_8-Net-(U1-A5): U1#13.5 (A5), U2#11.5 (A5), U3#10.5 (A5)
Board_8-Net-(U1-A6): U1#13.2 (A6), U2#11.2 (A6), U3#10.2 (A6)
Board_8-Net-(U1-A7): U1#13.4 (A7), U2#11.4 (A7), U3#10.4 (A7)
Board_8-Net-(U1-A): U1#13.3 (A), U2#11.3 (A), U3#10.3 (A)
Board_8-Net-(U1-GND): U1#13.8 (GND), U2#11.8 (GND), U3#10.8 (GND)
Board_8-Net-(U1-S0): U1#13.11 (S0), U2#11.11 (S0), U3#10.11 (S0)
Board_8-Net-(U1-S1): U1#13.10 (S1), U2#11.10 (S1), U3#10.10 (S1)
Board_8-Net-(U1-S2): U1#13.9 (S2), U2#11.9 (S2), U3#10.9 (S2)
Board_8-Net-(U1-VCC): U1#13.16 (VCC), U2#11.16 (VCC), U3#10.16 (VCC)
Board_8-Net-(U1-VEE): U1#13.7 (VEE), U2#11.7 (VEE), U3#10.7 (VEE)
Board_9-Net-(U1-*E): U1#12.6 (*E), U2#5.6 (*E), U3#12.6 (*E)
Board_9-Net-(U1-A0): U1#12.13 (A0), U2#5.13 (A0), U3#12.13 (A0)
Board_9-Net-(U1-A1): U1#12.14 (A1), U2#5.14 (A1), U3#12.14 (A1)
Board_9-Net-(U1-A2): U1#12.15 (A2), U2#5.15 (A2), U3#12.15 (A2)
Board_9-Net-(U1-A3): U1#12.12 (A3), U2#5.12 (A3), U3#12.12 (A3)
Board_9-Net-(U1-A4): U1#12.1 (A4), U2#5.1 (A4), U3#12.1 (A4)
Board_9-Net-(U1-A5): U1#12.5 (A5), U2#5.5 (A5), U3#12.5 (A5)
Board_9-Net-(U1-A6): U1#12.2 (A6), U2#5.2 (A6), U3#12.2 (A6)
Board_9-Net-(U1-A7): U1#12.4 (A7), U2#5.4 (A7), U3#12.4 (A7)
Board_9-Net-(U1-A): U1#12.3 (A), U2#5.3 (A), U3#12.3 (A)
Board_9-Net-(U1-GND): U1#12.8 (GND), U2#5.8 (GND), U3#12.8 (GND)
Board_9-Net-(U1-S0): U1#12.11 (S0), U2#5.11 (S0), U3#12.11 (S0)
Board_9-Net-(U1-S1): U1#12.10 (S1), U2#5.10 (S1), U3#12.10 (S1)
Board_9-Net-(U1-S2): U1#12.9 (S2), U2#5.9 (S2), U3#12.9 (S2)
Board_9-Net-(U1-VCC): U1#12.16 (VCC), U2#5.16 (VCC), U3#12.16 (VCC)
Board_9-Net-(U1-VEE): U1#12.7 (VEE), U2#5.7 (VEE), U3#12.7 (VEE)
Board_10-Net-(U1-*E): U1.6 (*E), U2#13.6 (*E), U3#8.6 (*E)
Board_10-Net-(U1-A0): U1.13 (A0), U2#13.13 (A0), U3#8.13 (A0)
Board_10-Net-(U1-A1): U1.14 (A1), U2#13.14 (A1), U3#8.14 (A1)
Board_10-Net-(U1-A2): U1.15 (A2), U2#13.15 (A2), U3#8.15 (A2)
Board_10-Net-(U1-A3): U1.12 (A3), U2#13.12 (A3), U3#8.12 (A3)
Board_10-Net-(U1-A4): U1.1 (A4), U2#13.1 (A4), U3#8.1 (A4)
Board_10-Net-(U1-A5): U1.5 (A5), U2#13.5 (A5), U3#8.5 (A5)
Board_10-Net-(U1-A6): U1.2 (A6), U2#13.2 (A6), U3#8.2 (A6)
Board_10-Net-(U1-A7): U1.4 (A7), U2#13.4 (A7), U3#8.4 (A7)
Board_10-Net-(U1-A): U1.3 (A), U2#13.3 (A), U3#8.3 (A)
Board_10-Net-(U1-GND): U1.8 (GND), U2#13.8 (GND), U3#8.8 (GND)
Board_10-Net-(U1-S0): U1.11 (S0), U2#13.11 (S0), U3#8.11 (S0)
Board_10-Net-(U1-S1): U1.10 (S1), U2#13.10 (S1), U3#8.10 (S1)
Board_10-Net-(U1-S2): U1.9 (S2), U2#13.9 (S2), U3#8.9 (S2)
Board_10-Net-(U1-VCC): U1.16 (VCC), U2#13.16 (VCC), U3#8.16 (VCC)
Board_10-Net-(U1-VEE): U1.7 (VEE), U2#13.7 (VEE), U3#8.7 (VEE)
Board_11-Net-(U1-*E): U1#6.6 (*E), U2#15.6 (*E), U3#4.6 (*E)
Board_11-Net-(U1-A0): U1#6.13 (A0), U2#15.13 (A0), U3#4.13 (A0)
Board_11-Net-(U1-A1): U1#6.14 (A1), U2#15.14 (A1), U3#4.14 (A1)
Board_11-Net-(U1-A2): U1#6.15 (A2), U2#15.15 (A2), U3#4.15 (A2)
Board_11-Net-(U1-A3): U1#6.12 (A3), U2#15.12 (A3), U3#4.12 (A3)
Board_11-Net-(U1-A4): U1#6.1 (A4), U2#15.1 (A4), U3#4.1 (A4)
Board_11-Net-(U1-A5): U1#6.5 (A5), U2#15.5 (A5), U3#4.5 (A5)
Board_11-Net-(U1-A6): U1#6.2 (A6), U2#15.2 (A6), U3#4.2 (A6)
Board_11-Net-(U1-A7): U1#6.4 (A7), U2#15.4 (A7), U3#4.4 (A7)
Board_11-Net-(U1-A): U1#6.3 (A), U2#15.3 (A), U3#4.3 (A)
Board_11-Net-(U1-GND): U1#6.8 (GND), U2#15.8 (GND), U3#4.8 (GND)
Board_11-Net-(U1-S0): U1#6.11 (S0), U2#15.11 (S0), U3#4.11 (S0)
Board_11-Net-(U1-S1): U1#6.10 (S1), U2#15.10 (S1), U3#4.10 (S1)
Board_11-Net-(U1-S2): U1#6.9 (S2), U2#15.9 (S2), U3#4.9 (S2)
Board_11-Net-(U1-VCC): U1#6.16 (VCC), U2#15.16 (VCC), U3#4.16 (VCC)
Board_11-Net-(U1-VEE): U1#6.7 (VEE), U2#15.7 (VEE), U3#4.7 (VEE)
Board_12-Net-(U1-*E): U1#15.6 (*E), U2#16.6 (*E), U3#15.6 (*E)
Board_12-Net-(U1-A0): U1#15.13 (A0), U2#16.13 (A0), U3#15.13 (A0)
Board_12-Net-(U1-A1): U1#15.14 (A1), U2#16.14 (A1), U3#15.14 (A1)
Board_12-Net-(U1-A2): U1#15.15 (A2), U2#16.15 (A2), U3#15.15 (A2)
Board_12-Net-(U1-A3): U1#15.12 (A3), U2#16.12 (A3), U3#15.12 (A3)
Board_12-Net-(U1-A4): U1#15.1 (A4), U2#16.1 (A4), U3#15.1 (A4)
Board_12-Net-(U1-A5): U1#15.5 (A5), U2#16.5 (A5), U3#15.5 (A5)
Board_12-Net-(U1-A6): U1#15.2 (A6), U2#16.2 (A6), U3#15.2 (A6)
Board_12-Net-(U1-A7): U1#15.4 (A7), U2#16.4 (A7), U3#15.4 (A7)
Board_12-Net-(U1-A): U1#15.3 (A), U2#16.3 (A), U3#15.3 (A)
Board_12-Net-(U1-GND): U1#15.8 (GND), U2#16.8 (GND), U3#15.8 (GND)
Board_12-Net-(U1-S0): U1#15.11 (S0), U2#16.11 (S0), U3#15.11 (S0)
Board_12-Net-(U1-S1): U1#15.10 (S1), U2#16.10 (S1), U3#15.10 (S1)
Board_12-Net-(U1-S2): U1#15.9 (S2), U2#16.9 (S2), U3#15.9 (S2)
Board_12-Net-(U1-VCC): U1#15.16 (VCC), U2#16.16 (VCC), U3#15.16 (VCC)
Board_12-Net-(U1-VEE): U1#15.7 (VEE), U2#16.7 (VEE), U3#15.7 (VEE)
Board_13-Net-(U1-*E): U1#8.6 (*E), U2#2.6 (*E), U3#16.6 (*E)
Board_13-Net-(U1-A0): U1#8.13 (A0), U2#2.13 (A0), U3#16.13 (A0)
Board_13-Net-(U1-A1): U1#8.14 (A1), U2#2.14 (A1), U3#16.14 (A1)
Board_13-Net-(U1-A2): U1#8.15 (A2), U2#2.15 (A2), U3#16.15 (A2)
Board_13-Net-(U1-A3): U1#8.12 (A3), U2#2.12 (A3), U3#16.12 (A3)
Board_13-Net-(U1-A4): U1#8.1 (A4), U2#2.1 (A4), U3#16.1 (A4)
Board_13-Net-(U1-A5): U1#8.5 (A5), U2#2.5 (A5), U3#16.5 (A5)
Board_13-Net-(U1-A6): U1#8.2 (A6), U2#2.2 (A6), U3#16.2 (A6)
Board_13-Net-(U1-A7): U1#8.4 (A7), U2#2.4 (A7), U3#16.4 (A7)
Board_13-Net-(U1-A): U1#8.3 (A), U2#2.3 (A), U3#16.3 (A)
Board_13-Net-(U1-GND): U1#8.8 (GND), U2#2.8 (GND), U3#16.8 (GND)
Board_13-Net-(U1-S0): U1#8.11 (S0), U2#2.11 (S0), U3#16.11 (S0)
Board_13-Net-(U1-S1): U1#8.10 (S1), U2#2.10 (S1), U3#16.10 (S1)
Board_13-Net-(U1-S2): U1#8.9 (S2), U2#2.9 (S2), U3#16.9 (S2)
Board_13-Net-(U1-VCC): U1#8.16 (VCC), U2#2.16 (VCC), U3#16.16 (VCC)
Board_13-Net-(U1-VEE): U1#8.7 (VEE), U2#2.7 (VEE), U3#16.7 (VEE)
Board_14-Net-(U1-*E): U1#9.6 (*E), U2#10.6 (*E), U3#3.6 (*E)
Board_14-Net-(U1-A0): U1#9.13 (A0), U2#10.13 (A0), U3#3.13 (A0)
Board_14-Net-(U1-A1): U1#9.14 (A1), U2#10.14 (A1), U3#3.14 (A1)
Board_14-Net-(U1-A2): U1#9.15 (A2), U2#10.15 (A2), U3#3.15 (A2)
Board_14-Net-(U1-A3): U1#9.12 (A3), U2#10.12 (A3), U3#3.12 (A3)
Board_14-Net-(U1-A4): U1#9.1 (A4), U2#10.1 (A4), U3#3.1 (A4)
Board_14-Net-(U1-A5): U1#9.5 (A5), U2#10.5 (A5), U3#3.5 (A5)
Board_14-Net-(U1-A6): U1#9.2 (A6), U2#10.2 (A6), U3#3.2 (A6)
Board_14-Net-(U1-A7): U1#9.4 (A7), U2#10.4 (A7), U3#3.4 (A7)
Board_14-Net-(U1-A): U1#9.3 (A), U2#10.3 (A), U3#3.3 (A)
Board_14-Net-(U1-GND): U1#9.8 (GND), U2#10.8 (GND), U3#3.8 (GND)
Board_14-Net-(U1-S0): U1#9.11 (S0), U2#10.11 (S0), U3#3.11 (S0)
Board_14-Net-(U1-S1): U1#9.10 (S1), U2#10.10 (S1), U3#3.10 (S1)
Board_14-Net-(U1-S2): U1#9.9 (S2), U2#10.9 (S2), U3#3.9 (S2)
Board_14-Net-(U1-VCC): U1#9.16 (VCC), U2#10.16 (VCC), U3#3.16 (VCC)
Board_14-Net-(U1-VEE): U1#9.7 (VEE), U2#10.7 (VEE), U3#3.7 (VEE)
Board_15-Net-(U1-*E): U1#4.6 (*E), U2#3.6 (*E), U3#2.6 (*E)
Board_15-Net-(U1-A0): U1#4.13 (A0), U2#3.13 (A0), U3#2.13 (A0)
Board_15-Net-(U1-A1): U1#4.14 (A1), U2#3.14 (A1), U3#2.14 (A1)
Board_15-Net-(U1-A2): U1#4.15 (A2), U2#3.15 (A2), U3#2.15 (A2)
Board_15-Net-(U1-A3): U1#4.12 (A3), U2#3.12 (A3), U3#2.12 (A3)
Board_15-Net-(U1-A4): U1#4.1 (A4), U2#3.1 (A4), U3#2.1 (A4)
Board_15-Net-(U1-A5): U1#4.5 (A5), U2#3.5 (A5), U3#2.5 (A5)
Board_15-Net-(U1-A6): U1#4.2 (A6), U2#3.2 (A6), U3#2.2 (A6)
Board_15-Net-(U1-A7): U1#4.4 (A7), U2#3.4 (A7), U3#2.4 (A7)
Board_15-Net-(U1-A): U1#4.3 (A), U2#3.3 (A), U3#2.3 (A)
Board_15-Net-(U1-GND): U1#4.8 (GND), U2#3.8 (GND), U3#2.8 (GND)
Board_15-Net-(U1-S0): U1#4.11 (S0), U2#3.11 (S0), U3#2.11 (S0)
Board_15-Net-(U1-S1): U1#4.10 (S1), U2#3.10 (S1), U3#2.10 (S1)
Board_15-Net-(U1-S2): U1#4.9 (S2), U2#3.9 (S2), U3#2.9 (S2)
Board_15-Net-(U1-VCC): U1#4.16 (VCC), U2#3.16 (VCC), U3#2.16 (VCC)
Board_15-Net-(U1-VEE): U1#4.7 (VEE), U2#3.7 (VEE), U3#2.7 (VEE)
