AnotherBuildCorner/Relay_Switcher/PCB's/Loop Board V3 Jackless/Loop Board 3 Jackless Input/Jackless-Panel/Jackless-Panel.kicad_pcb

## KiCad design PCB's/Loop Board V3 Jackless/Loop Board 3 Jackless Input/Jackless-Panel/Jackless-Panel.kicad_pcb (2024-06-10)

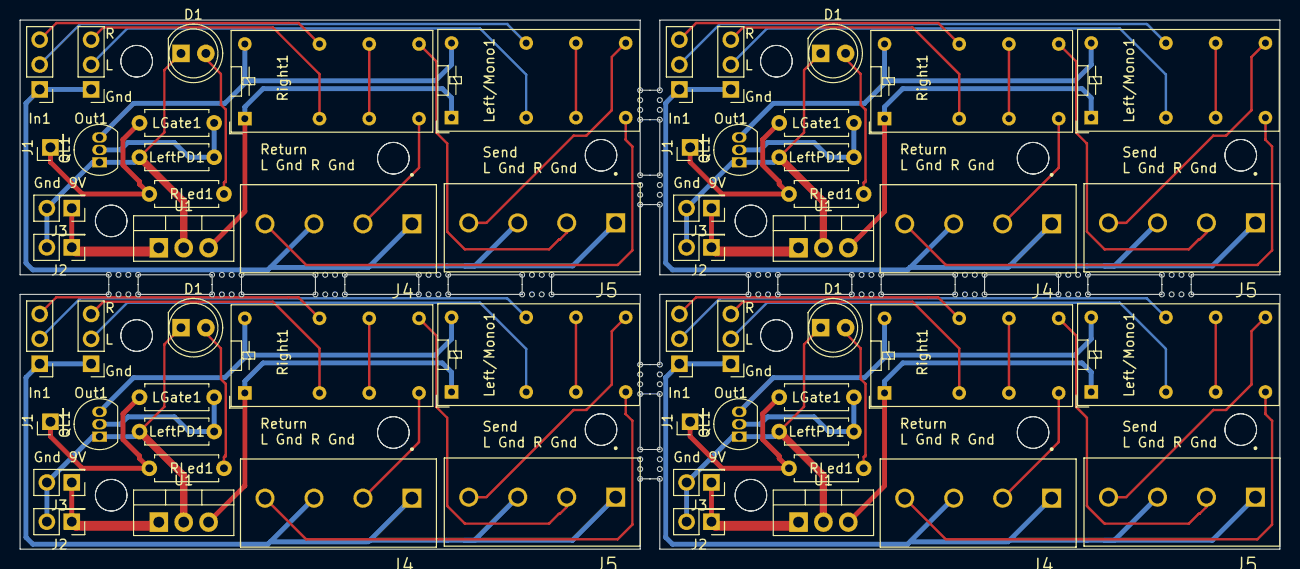
[picture p67: board Jackless-Panel.kicad_pcb from above]

Board: 2 copper layers, 128.6 x 54.0 mm, 172 parts (0 on the bottom side), 72 nets.

Parts:
D1, D1#2, D1#3, D1#4: LED; LED_D5.0mm
In1, In1#2, In1#3, In1#4: Conn_01x03_Pin; PinHeader_1x03_P2.54mm_Vertical
J1, J1#2, J1#3, J1#4: Conn_01x01_Pin; PinHeader_1x01_P2.54mm_Vertical
J2, J2#2, J2#3, J2#4, J3, J3#2, J3#3, J3#4: Conn_01x02_Pin; PinHeader_2x01_P2.54mm_Vertical
J4, J4#2, J4#3, J4#4, J5, J5#2, J5#3, J5#4: Screw_Terminal_01x04; CUI_TB001-500-04BE
KiKit_MB_1_1, KiKit_MB_1_2, KiKit_MB_1_3, KiKit_MB_1_4, KiKit_MB_2_1, KiKit_MB_2_2, KiKit_MB_2_3, KiKit_MB_2_4, KiKit_MB_3_1, KiKit_MB_3_2, KiKit_MB_3_3, KiKit_MB_3_4, KiKit_MB_4_1, KiKit_MB_4_2, KiKit_MB_4_3, KiKit_MB_4_4, KiKit_MB_5_1, KiKit_MB_5_2, KiKit_MB_5_3, KiKit_MB_5_4, KiKit_MB_6_1, KiKit_MB_6_2, KiKit_MB_6_3, KiKit_MB_6_4, KiKit_MB_7_1, KiKit_MB_7_2, KiKit_MB_7_3, KiKit_MB_7_4, KiKit_MB_8_1, KiKit_MB_8_2, KiKit_MB_8_3, KiKit_MB_8_4, KiKit_MB_9_1, KiKit_MB_9_2, KiKit_MB_9_3, KiKit_MB_9_4, KiKit_MB_10_1, KiKit_MB_10_2, KiKit_MB_10_3, KiKit_MB_10_4, KiKit_MB_11_1, KiKit_MB_11_2, KiKit_MB_11_3, KiKit_MB_11_4, KiKit_MB_12_1, KiKit_MB_12_2, KiKit_MB_12_3, KiKit_MB_12_4, KiKit_MB_13_1, KiKit_MB_13_2, KiKit_MB_13_3, KiKit_MB_13_4, KiKit_MB_14_1, KiKit_MB_14_2, KiKit_MB_14_3, KiKit_MB_14_4, KiKit_MB_15_1, KiKit_MB_15_2, KiKit_MB_15_3, KiKit_MB_15_4, KiKit_MB_16_1, KiKit_MB_16_2, KiKit_MB_16_3, KiKit_MB_16_4, KiKit_MB_17_1, KiKit_MB_17_2, KiKit_MB_17_3, KiKit_MB_17_4, KiKit_MB_18_1, KiKit_MB_18_2, KiKit_MB_18_3, KiKit_MB_18_4, KiKit_MB_19_1, KiKit_MB_19_2, KiKit_MB_19_3, KiKit_MB_19_4, KiKit_MB_20_1, KiKit_MB_20_2, KiKit_MB_20_3, KiKit_MB_20_4, KiKit_MB_21_1, KiKit_MB_21_2, KiKit_MB_21_3, KiKit_MB_21_4, KiKit_MB_22_1, KiKit_MB_22_2, KiKit_MB_22_3, KiKit_MB_22_4, KiKit_MB_23_1, KiKit_MB_23_2, KiKit_MB_23_3, KiKit_MB_23_4, KiKit_MB_24_1, KiKit_MB_24_2, KiKit_MB_24_3, KiKit_MB_24_4, KiKit_MB_25_1, KiKit_MB_25_2, KiKit_MB_25_3, KiKit_MB_25_4, KiKit_MB_26_1, KiKit_MB_26_2, KiKit_MB_26_3, KiKit_MB_26_4, KiKit_MB_27_1, KiKit_MB_27_2, KiKit_MB_27_3, KiKit_MB_27_4, KiKit_MB_28_1, KiKit_MB_28_2, KiKit_MB_28_3, KiKit_MB_28_4: NPTH
LGate1, LGate1#2, LGate1#3, LGate1#4: R; R_Axial_DIN0207_L6.3mm_D2.5mm_P7.62mm_Horizontal
Left/Mono1, Left/Mono1#2, Left/Mono1#3, Left/Mono1#4: G5V-2; Relay_DPDT_Omron_G5V-2
LeftPD1, LeftPD1#2, LeftPD1#3, LeftPD1#4: R; R_Axial_DIN0207_L6.3mm_D2.5mm_P7.62mm_Horizontal
Out1, Out1#2, Out1#3, Out1#4: Conn_01x03_Pin; PinHeader_1x03_P2.54mm_Vertical
QL1, QL1#2, QL1#3, QL1#4: 2N7000; TO-92_Inline
RLed1, RLed1#2, RLed1#3, RLed1#4: 100; R_Axial_DIN0207_L6.3mm_D2.5mm_P7.62mm_Horizontal
Right1, Right1#2, Right1#3, Right1#4: G5V-2; Relay_DPDT_Omron_G5V-2
U1, U1#2, U1#3, U1#4: L7805; TO-220-3_Vertical

Connections:
Board_0-/5V: Left/Mono1#3.1, Right1.1, U1#2.3 (OUT)
Board_0-/9V: J2#2.1, J3#2.1, U1#2.1 (IN)
Board_0-/Control: J1#4.1, LGate1#4.1, RLed1#4.1
Board_0-/Ctrl_GND: D1#3.1 (K), J2#2.2, J3#2.2, LeftPD1#2.2, QL1#4.1 (S), U1#2.2 (GND)
Board_0-/L_Return: J4#3.4, Left/Mono1#3.8
Board_0-/L_Send: J5#4.4, Left/Mono1#3.9
Board_0-/L_in: In1#2.2, Left/Mono1#3.13
Board_0-/L_out: Left/Mono1#3.4, Out1.2
Board_0-/R_Return: J4#3.2, Right1.8
Board_0-/R_in: In1#2.3, Right1.13
Board_0-/R_out: Out1.3, Right1.4
Board_0-/R_send: J5#4.2, Right1.9
Board_0-/Signal_Gnd: In1#2.1, J4#3.1, J4#3.3, J5#4.1, J5#4.3, Out1.1
Board_0-Net-(D1-A): D1#3.2 (A), RLed1#4.2
Board_0-Net-(Left/Mono1-Pad11): Left/Mono1#3.6, Left/Mono1#3.11
Board_0-Net-(QL1-D): Left/Mono1#3.16, QL1#4.3 (D), Right1.16
Board_0-Net-(QL1-G): LGate1#4.2, LeftPD1#2.1, QL1#4.2 (G)
Board_0-Net-(Right1-Pad11): Right1.6, Right1.11
Board_1-/5V: Left/Mono1#2.1, Right1#2.1, U1.3 (OUT)
Board_1-/9V: J2#3.1, J3.1, U1.1 (IN)
Board_1-/Control: J1#3.1, LGate1#2.1, RLed1.1
Board_1-/Ctrl_GND: D1#2.1 (K), J2#3.2, J3.2, LeftPD1#3.2, QL1#2.1 (S), U1.2 (GND)
Board_1-/L_Return: J4#4.4, Left/Mono1#2.8
Board_1-/L_Send: J5.4, Left/Mono1#2.9
Board_1-/L_in: In1.2, Left/Mono1#2.13
Board_1-/L_out: Left/Mono1#2.4, Out1#2.2
Board_1-/R_Return: J4#4.2, Right1#2.8
Board_1-/R_in: In1.3, Right1#2.13
Board_1-/R_out: Out1#2.3, Right1#2.4
Board_1-/R_send: J5.2, Right1#2.9
Board_1-/Signal_Gnd: In1.1, J4#4.1, J4#4.3, J5.1, J5.3, Out1#2.1
Board_1-Net-(D1-A): D1#2.2 (A), RLed1.2
Board_1-Net-(Left/Mono1-Pad11): Left/Mono1#2.6, Left/Mono1#2.11
Board_1-Net-(QL1-D): Left/Mono1#2.16, QL1#2.3 (D), Right1#2.16
Board_1-Net-(QL1-G): LGate1#2.2, LeftPD1#3.1, QL1#2.2 (G)
Board_1-Net-(Right1-Pad11): Right1#2.6, Right1#2.11
Board_2-/5V: Left/Mono1.1, Right1#4.1, U1#3.3 (OUT)
Board_2-/9V: J2#4.1, J3#4.1, U1#3.1 (IN)
Board_2-/Control: J1#2.1, LGate1.1, RLed1#2.1
Board_2-/Ctrl_GND: D1.1 (K), J2#4.2, J3#4.2, LeftPD1#4.2, QL1#3.1 (S), U1#3.2 (GND)
Board_2-/L_Return: J4#2.4, Left/Mono1.8
Board_2-/L_Send: J5#2.4, Left/Mono1.9
Board_2-/L_in: In1#4.2, Left/Mono1.13
Board_2-/L_out: Left/Mono1.4, Out1#4.2
Board_2-/R_Return: J4#2.2, Right1#4.8
Board_2-/R_in: In1#4.3, Right1#4.13
Board_2-/R_out: Out1#4.3, Right1#4.4
Board_2-/R_send: J5#2.2, Right1#4.9
Board_2-/Signal_Gnd: In1#4.1, J4#2.1, J4#2.3, J5#2.1, J5#2.3, Out1#4.1
Board_2-Net-(D1-A): D1.2 (A), RLed1#2.2
Board_2-Net-(Left/Mono1-Pad11): Left/Mono1.6, Left/Mono1.11
Board_2-Net-(QL1-D): Left/Mono1.16, QL1#3.3 (D), Right1#4.16
Board_2-Net-(QL1-G): LGate1.2, LeftPD1#4.1, QL1#3.2 (G)
Board_2-Net-(Right1-Pad11): Right1#4.6, Right1#4.11
Board_3-/5V: Left/Mono1#4.1, Right1#3.1, U1#4.3 (OUT)
Board_3-/9V: J2.1, J3#3.1, U1#4.1 (IN)
Board_3-/Control: J1.1, LGate1#3.1, RLed1#3.1
Board_3-/Ctrl_GND: D1#4.1 (K), J2.2, J3#3.2, LeftPD1.2, QL1.1 (S), U1#4.2 (GND)
Board_3-/L_Return: J4.4, Left/Mono1#4.8
Board_3-/L_Send: J5#3.4, Left/Mono1#4.9
Board_3-/L_in: In1#3.2, Left/Mono1#4.13
Board_3-/L_out: Left/Mono1#4.4, Out1#3.2
Board_3-/R_Return: J4.2, Right1#3.8
Board_3-/R_in: In1#3.3, Right1#3.13
Board_3-/R_out: Out1#3.3, Right1#3.4
Board_3-/R_send: J5#3.2, Right1#3.9
Board_3-/Signal_Gnd: In1#3.1, J4.1, J4.3, J5#3.1, J5#3.3, Out1#3.1
Board_3-Net-(D1-A): D1#4.2 (A), RLed1#3.2
Board_3-Net-(Left/Mono1-Pad11): Left/Mono1#4.6, Left/Mono1#4.11
Board_3-Net-(QL1-D): Left/Mono1#4.16, QL1.3 (D), Right1#3.16
Board_3-Net-(QL1-G): LGate1#3.2, LeftPD1.1, QL1.2 (G)
Board_3-Net-(Right1-Pad11): Right1#3.6, Right1#3.11
